mikespook/ProofBox/src/tinyproofbox/Relay.h

#ifndef TPB_RELAY_H
#define TPB_RELAY_H

#include <Arduino.h>

class RelayClass {
	public:
		const static uint8_t PinHeater = 8;
		const static uint8_t PinFan = 7;

		RelayClass(int pin);
		void off();		
		void on();
		bool isOn();
		
	private:
		int _pin;
		int _state;
};

static RelayClass Heater(RelayClass::PinHeater);
static RelayClass Fan(RelayClass::PinFan);

#endif
